smwalke83/GardenNomad/Drawings+Notes+Flowcharts/GN_Notes_4.pdf

J ,

## PCts RoUP^;"[t

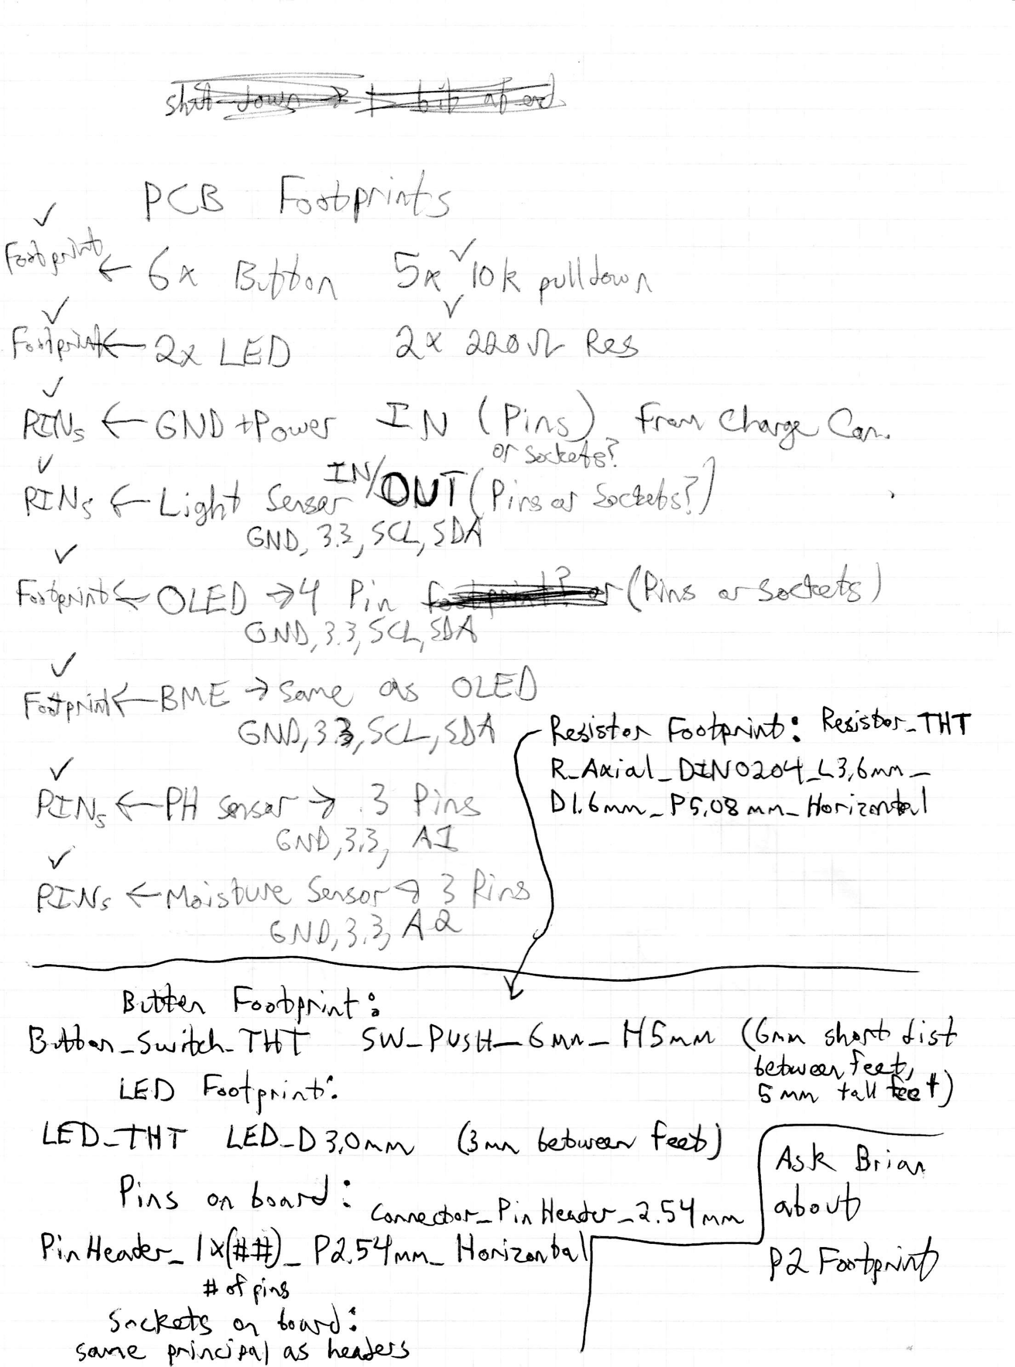
[picture p1: page 1]

# f"ftdfr<- (n B.bi^,\ Ex{nkp,,ti[*x

# f",6"f- a* LgD fx s[b,n ?e&

d\,, (^e Nb +poua.r -r.51 (^fi",r). fu %u-e*.

t/

# ENs ?L,ehtr k#/Qt{l (il,Iff]"u,r/ }

### v '" GNDil*r5Q/504

## fi,{^,NtaOLED eI P,'^ f#-:fi- ".(P** "rs".**{t)

\/

## -orll

| ,? J,,SrL,s,i( '
f.ir*d#Bt*E ?A? 3 :f0,, n ), .,. p,.,r*.,

## GM, 3Ar1(LttI4 ,- K"*,rt4.r Fo"h^:**: fuj*sr-fllf

## PcN, <-Pii gwr ) ,1 P;na \ b t,(^

PF,oB - | ^,,.-fh.;z.n&ul

## GruD ,r,,, AA \

\/. | Gxrb,3,3, A{

### PG.Afr <-Ma.>buJt, L''sora. ? R't'a

G^Jr, 3 ), A,L

### g rtfu^ F.",llr.)^f ', v

## B*l* -5*,LA-THT S^J--Ptri tJ- ( rt^ - H 9,n*

LED t.-[fni,,$,.
LfD JH T LED - D 3,o \A, (S *^" 6eA,^rec-./ P**)

(6".^ sh,.n6 J;s] 'LQ}Aaalr,-/^.,

# E ;;?"[ ta fJ

Pins on Ao^"J : comqcbor* p;^ Hon+.r-?.s.1 *n-

# Pl,. He^&-- I x[++)- ? a,r1 *^- H"^iz*$."\F-

+ "t gi"f

## !.a-po[ h {.\\t*) :

9o,^^e- |ninct *t) ovS hzdArj

A.r I< B, ) an
^L'h

# Pr- F^+;il
