smwalke83/GardenNomad/Drawings+Notes+Flowcharts/Capstone Flowcharts.pdf

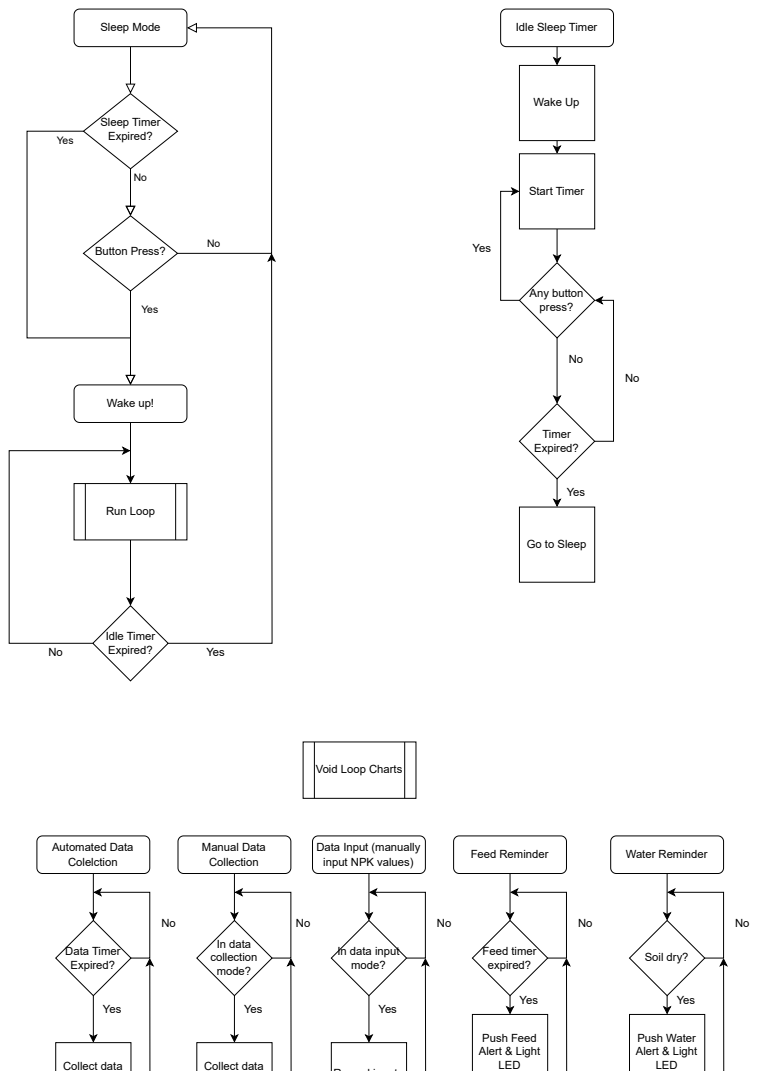
[picture p2: page 1]
Sleep Mode; Yes; Sleep Timer Expired?; Wake up!; Run Loop; Idle Timer; Expired?; Automated Data Colelction; Data Timer Expired?; Collect data; Manual Data Collection; In data collection mode?; Feed Reminder; Feed timer expired?; Push Feed Alert & Light LED; Water Reminder; Soil dry?; Push Water Alert & Light LED; Wake Up; Any button press?; Start Timer; Timer Expired?

Idle Sleep Timer

No Button Press?

Go to Sleep

Void Loop Charts

Data Input (manually
input NPK values)

In data input
mode?

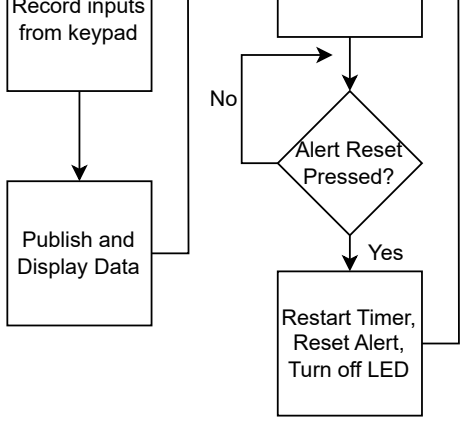
[picture p3: figure]
Record inputs from keypad; Publish and Display Data; Alert Reset Pressed?; Restart Timer, Reset Alert, Turn off LED; Yes

Co ect data
(automatic
sensors only)

Publish and
Display Data

Reset Data
Timer

Co ect data
(manual PH
sensor)

Publish and
Display Data

Alert Reset
Pressed?

Reset Alert,
Turn off LED

No

Yes
