smwalke83/GardenNomad/Drawings+Notes+Flowcharts/GN_Flowcharts_2.pdf

# lEc,qr+\

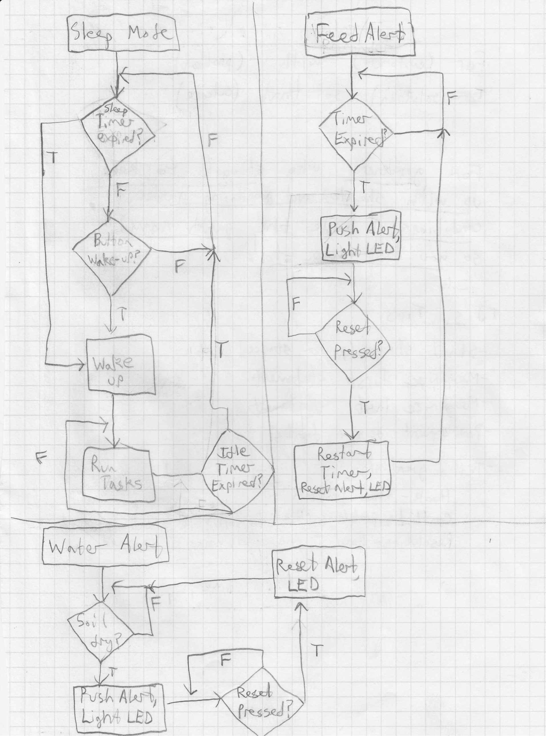
[picture p14: page 1]

\P"r#9

Re6+"^+
f ir^er;
Ru* tl^nl.,t

nuyjl,

e,f Ate'i I
