smwalke83/GardenNomad/Drawings+Notes+Flowcharts/GN_Notes_1.pdf

# ffi

N,v

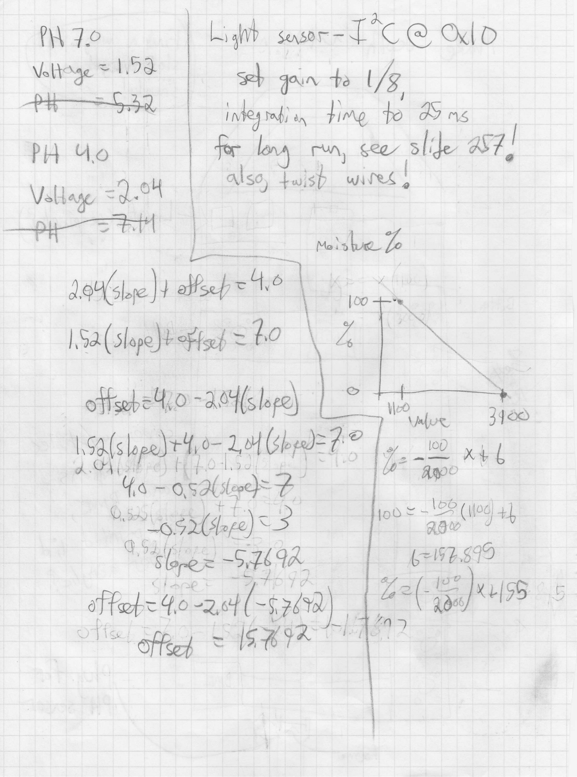
[picture p15: page 1]

V"L{age

?\\ 7"c
G[]'..Jq = [,5&

f i."+ Ll.o

## at;)*'Nl:

## L,th$ s*\bpr-{^C g Q,t O

5+ Za*ry 4a t /8 ,

### ', rqndi ,n l',r9 t"

## fu l*4 ffir

e,lssr T*;5f urred j

x+ (

roo : -\Y2 ( rlur, *1

4 8,\/, | <t | v
,t.u rjl.
L'=tE|,518

# il=(ff") (rte5 t- ufI*t

1

## -f*oQ,o -3,0{(lt.*i L:

Lgo.(s l^ ri.Lt, o*,1-,4 Gi, Qa/ o
J ul,. ' i
, -'1,,-, I

# (,a - o,s;i:ir,"4:| ; (')i '"':ogl?bi,4tt j

ii - | I

-' ''s'f*.=€

# . -i,+{i.ln i

t*:"\,c*7"
#v+=4ub | lw

| 7
"gr# =?,0
