smwalke83/GardenNomad/Drawings+Notes+Flowcharts/GN_Notes_2.pdf

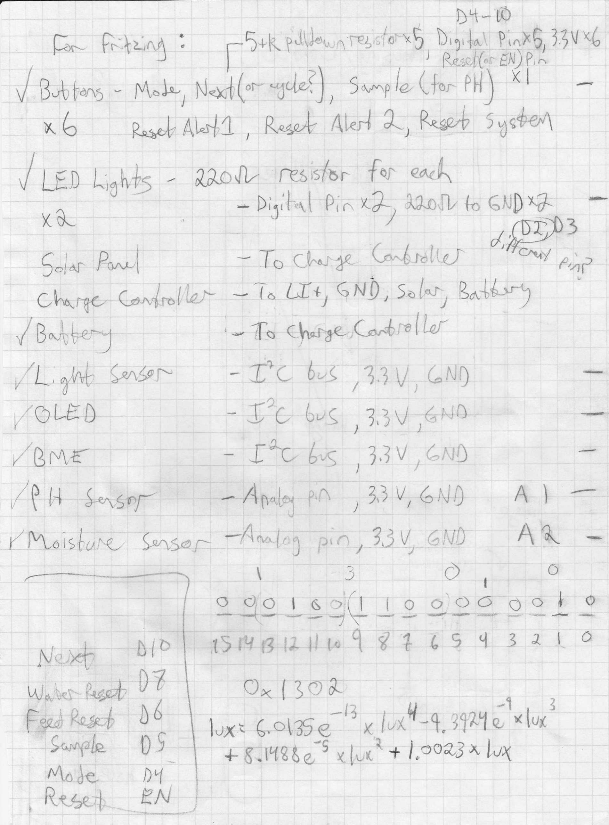
[picture p16: page 1]

Dt*r0
E"= G"l*g

I S, Ls[]s ' aaoJL res'sfu' f'r t*(
x0..- . K$' | * >iriht P; n"7) / ie*'ll'u *:m
| ,rD-I')}
5.1* P-* ,t | - To CLo",#- L*.^'droii*,t a'Kt r*f

Ct*rye' G^{* I e-r- - To E+t C N' ., 5u ldJ B"{d""-7
i g"ib"l | '* To clBry€.''(-*+ ;rlV

### / o go rsrl(t to o,oo oo I a

| - -t-

G-
-Y
:* € <- | * | F;. '*..- | 4
I5{!lgtilJ lc'l d+ L 9 ''{ 3 e I o

## Nt'xl ff:l l5{!rglilJ lc'l 'l+ L e'{ 3 e I

w,rri.,i f*6*+ *7 \ a^t3.:&

*-----*-) \ | 3 | c
,
u

4o Je D'|

+ $-ttt8&e' t iri' * l,'tv<'5 a i* *,4,t, l{ \ luxr 6""t3, u', ri,^il-1. r?r1 n.'*t,*'
$."upf* 0 ! \ ;,g;,Te&ui r{",r:t + l.c,oa1x lu{

,

It tg,: ,i EN ,
