smwalke83/GardenNomad/Drawings+Notes+Flowcharts/GN_Notes_3.pdf

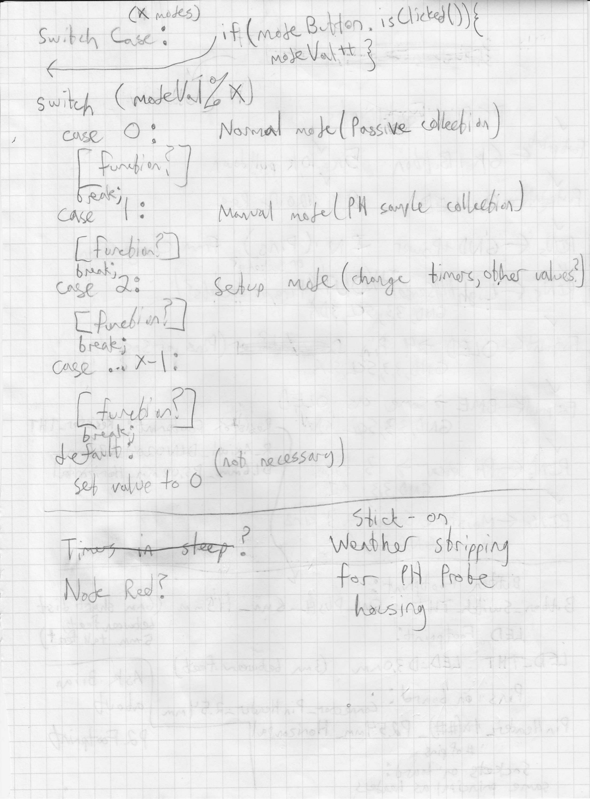
[picture p17: page 1]

(K ,'""Jes)
S*, .i'h L** '.
,);4 ⁽ *;-U*Wx)

5-f' .l- -
U*^t hlr

## f"- fH

l^-av, rn'q
)

cl\
s{r;,,,y
P*Le

'

,)
(,
